ZeshuLiu/SX-70-Mk2/Hardwares/PowerBack/Case/PCB3D/ASM.SLDASM

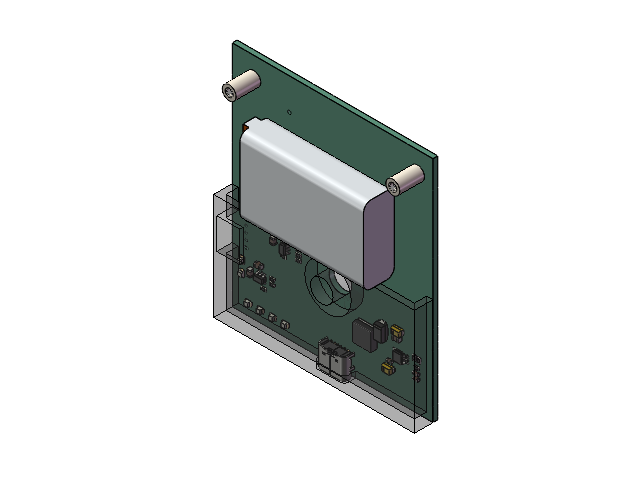
[picture p23: CAD file, 2024-09-11]
Hardwares/PowerBack/Case/PCB3D/ASM.SLDASM
C_0805_2012Metric-0.step x 4
C_0603_1608Metric-1.step x 3
L_Cenker_CKCS6020-2.step
D_SMA-3.step
R_0603_1608Metric-4.step x 10
USB_C_Receptacle_GCT_USB4125-xx-x_6P_TopMnt_Horizontal.step
SOT_23_6.step x 2
CP_EIA_3216_18_Kemet_A.step x 2
LED_0805_2012Metric-5.step x 6
VSSOP_8_30x30mm_P065mm.step
sx70battery_PCB.step
102540Battery
贴片螺母M2.5-H8-D3 x 2
Case10mmBat
