ZeshuLiu/SX-70-Mk2/Hardwares/Body_controller/Rev1/3D_v2/BodyControllerAsm.SLDASM

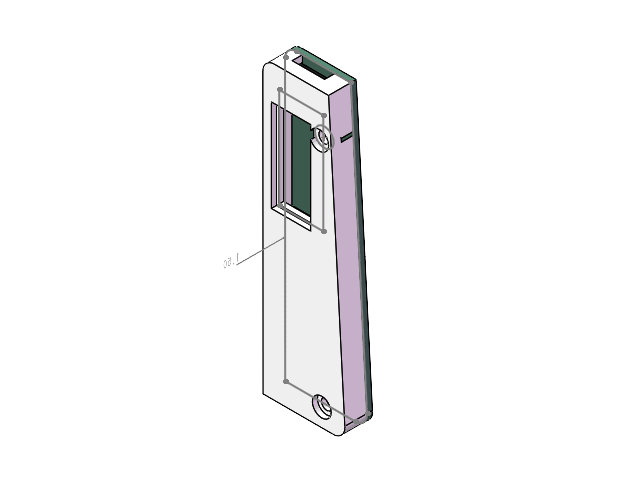
[picture p24: CAD file, 2024-03-19]
Hardwares/Body_controller/Rev1/3D_v2/BodyControllerAsm.SLDASM
C_0603_1608Metric-0.step x 12
TE_84953_6.step
SSOP_20_44x65mm_P065mm.step
R_0603_1608Metric-1.step x 5
PinHeader_1x03_P254mm_Horizontal.step
R_0805_2012Metric-2.step x 2
Controller_body_PCB.step
ControllerCase
